Skwiggums/Shirdal-P4/step/Common components/shirdalfwcsep v21.step

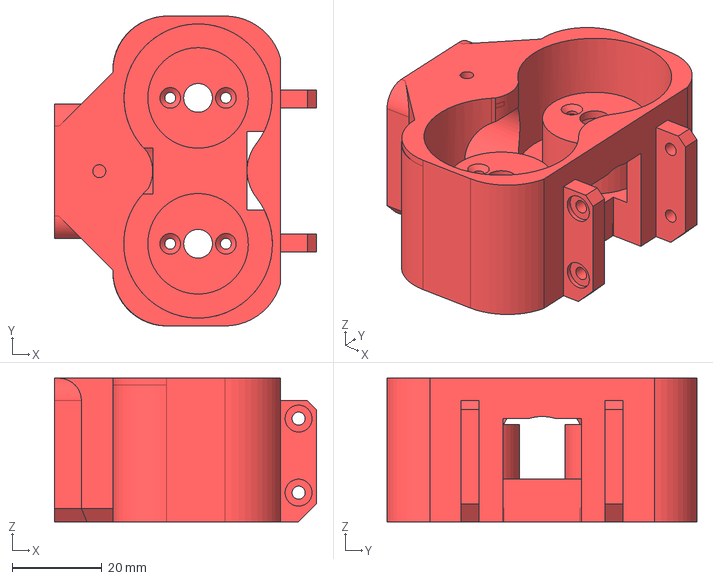
[picture p18: CAD file, 2022-11-20]
step/Common components/shirdalfwcsep v21.step
58.4 x 69.1 x 32.0 mm
