Skwiggums/Shirdal-P4/stls/Common components/top motor cover.stl

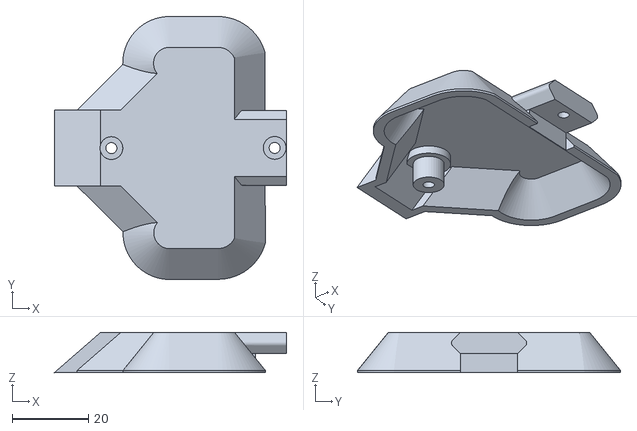
[picture p19: CAD file, 2022-11-20]
stls/Common components/top motor cover.stl
61.1 x 69.1 x 10.6
