Skwiggums/Shirdal-P4/stls/Common components/magwell.stl

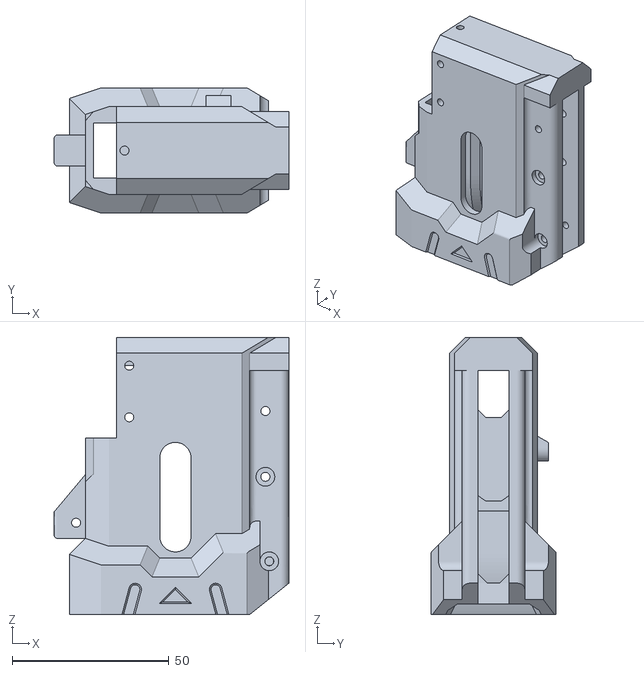
[picture p20: CAD file, 2022-11-20]
stls/Common components/magwell.stl
75.0 x 40.0 x 88.5
