Skwiggums/Shirdal-P4/step/Common components/shirdalgripscaleleft v10.step

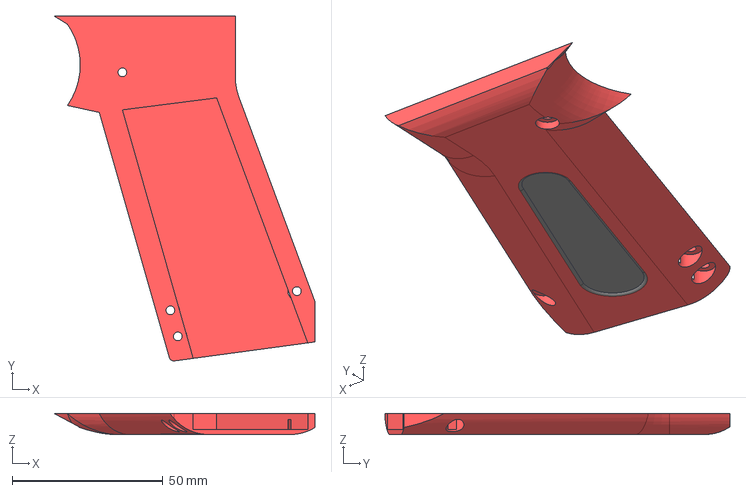
[picture p21: CAD file, 2022-11-20]
step/Common components/shirdalgripscaleleft v10.step
86.7 x 114.5 x 7.00 mm
