Skwiggums/Shirdal-P4/stls/Common components/mag release.stl

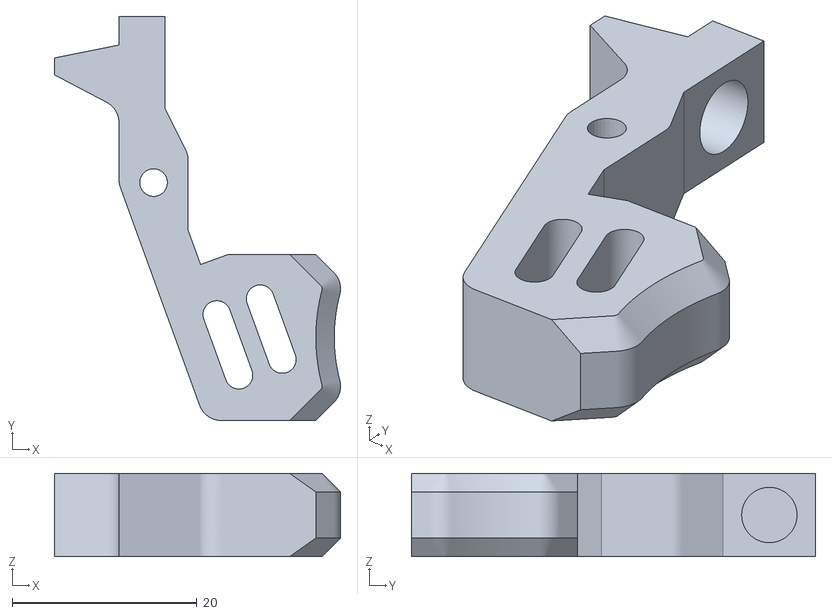
[picture p22: CAD file, 2022-11-20]
stls/Common components/mag release.stl
31.0 x 43.8 x 9.00
