Skwiggums/Shirdal-P4/step/Common components/flashhider3 v1.step

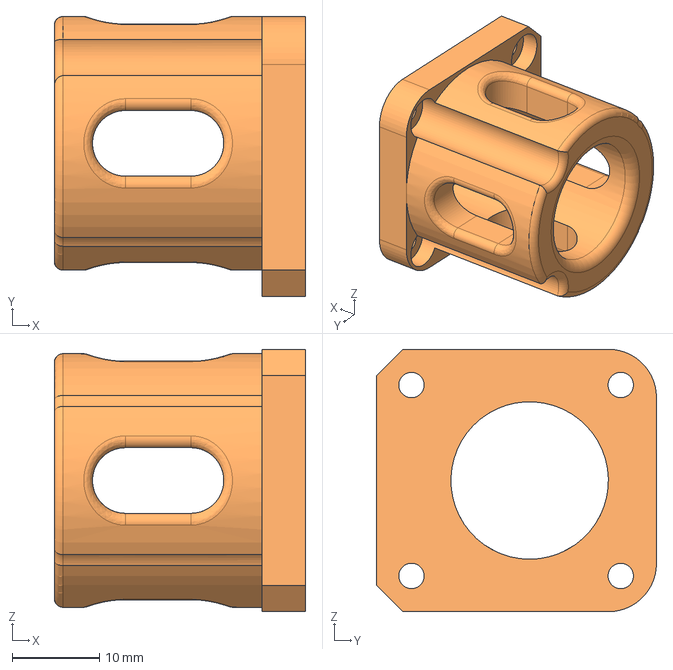
[picture p23: CAD file, 2022-11-20]
step/Common components/flashhider3 v1.step
28.8 x 32.0 x 30.0 mm
