Skwiggums/Shirdal-P4/stls/Common components/Grip core.stl

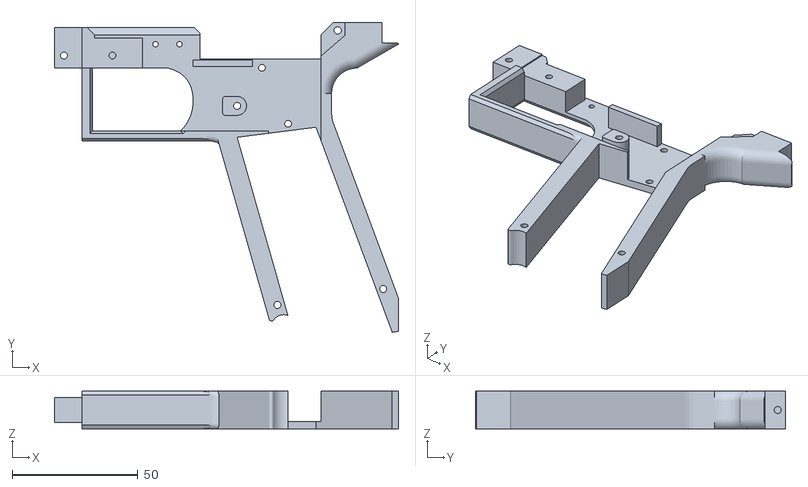
[picture p24: CAD file, 2022-11-20]
stls/Common components/Grip core.stl
136.5 x 122.9 x 15.0
