Skwiggums/Shirdal-P4/stls/Common components/battery cap.stl

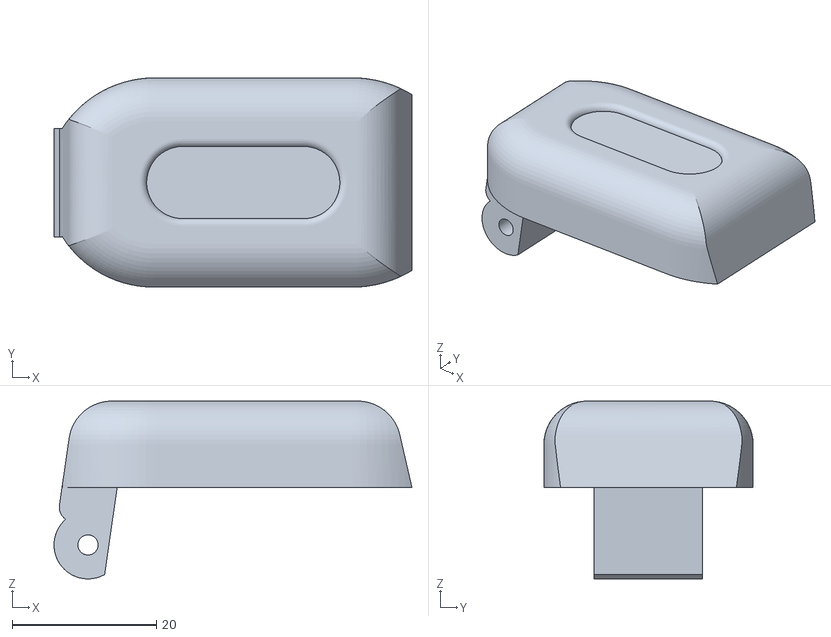
[picture p25: CAD file, 2022-11-20]
stls/Common components/battery cap.stl
49.6 x 29.0 x 24.6
