Skwiggums/Shirdal-P4/step/Common components/shirdalgripcover v28.step

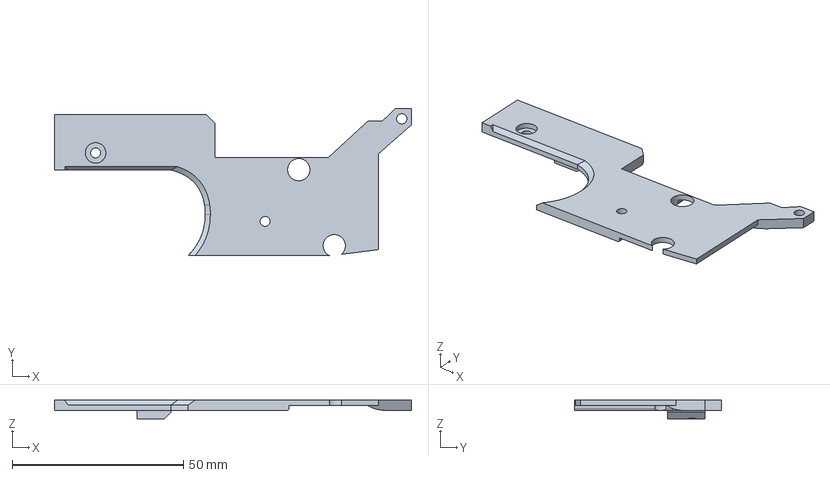
[picture p26: CAD file, 2022-11-20]
step/Common components/shirdalgripcover v28.step
104.2 x 43.0 x 5.50 mm
