Skwiggums/Shirdal-P4/stls/Common components/SF lever.stl

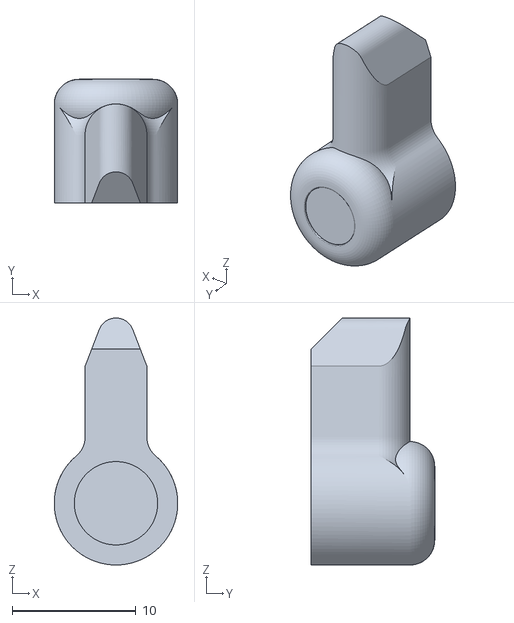
[picture p27: CAD file, 2022-11-20]
stls/Common components/SF lever.stl
10.00 x 10.0 x 20.0
