Skwiggums/Shirdal-P4/step/Common components/select fire lever v4.step

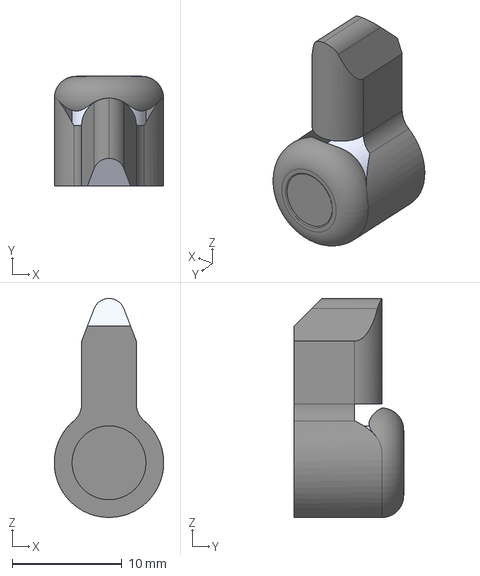
[picture p28: CAD file, 2022-11-20]
step/Common components/select fire lever v4.step
10.00 x 10.0 x 20.0 mm
